diskman88/mpython-shield1/1_Hardware/V1.3/V1.3/掌控拓展板Ⅰ V1.2.pdf

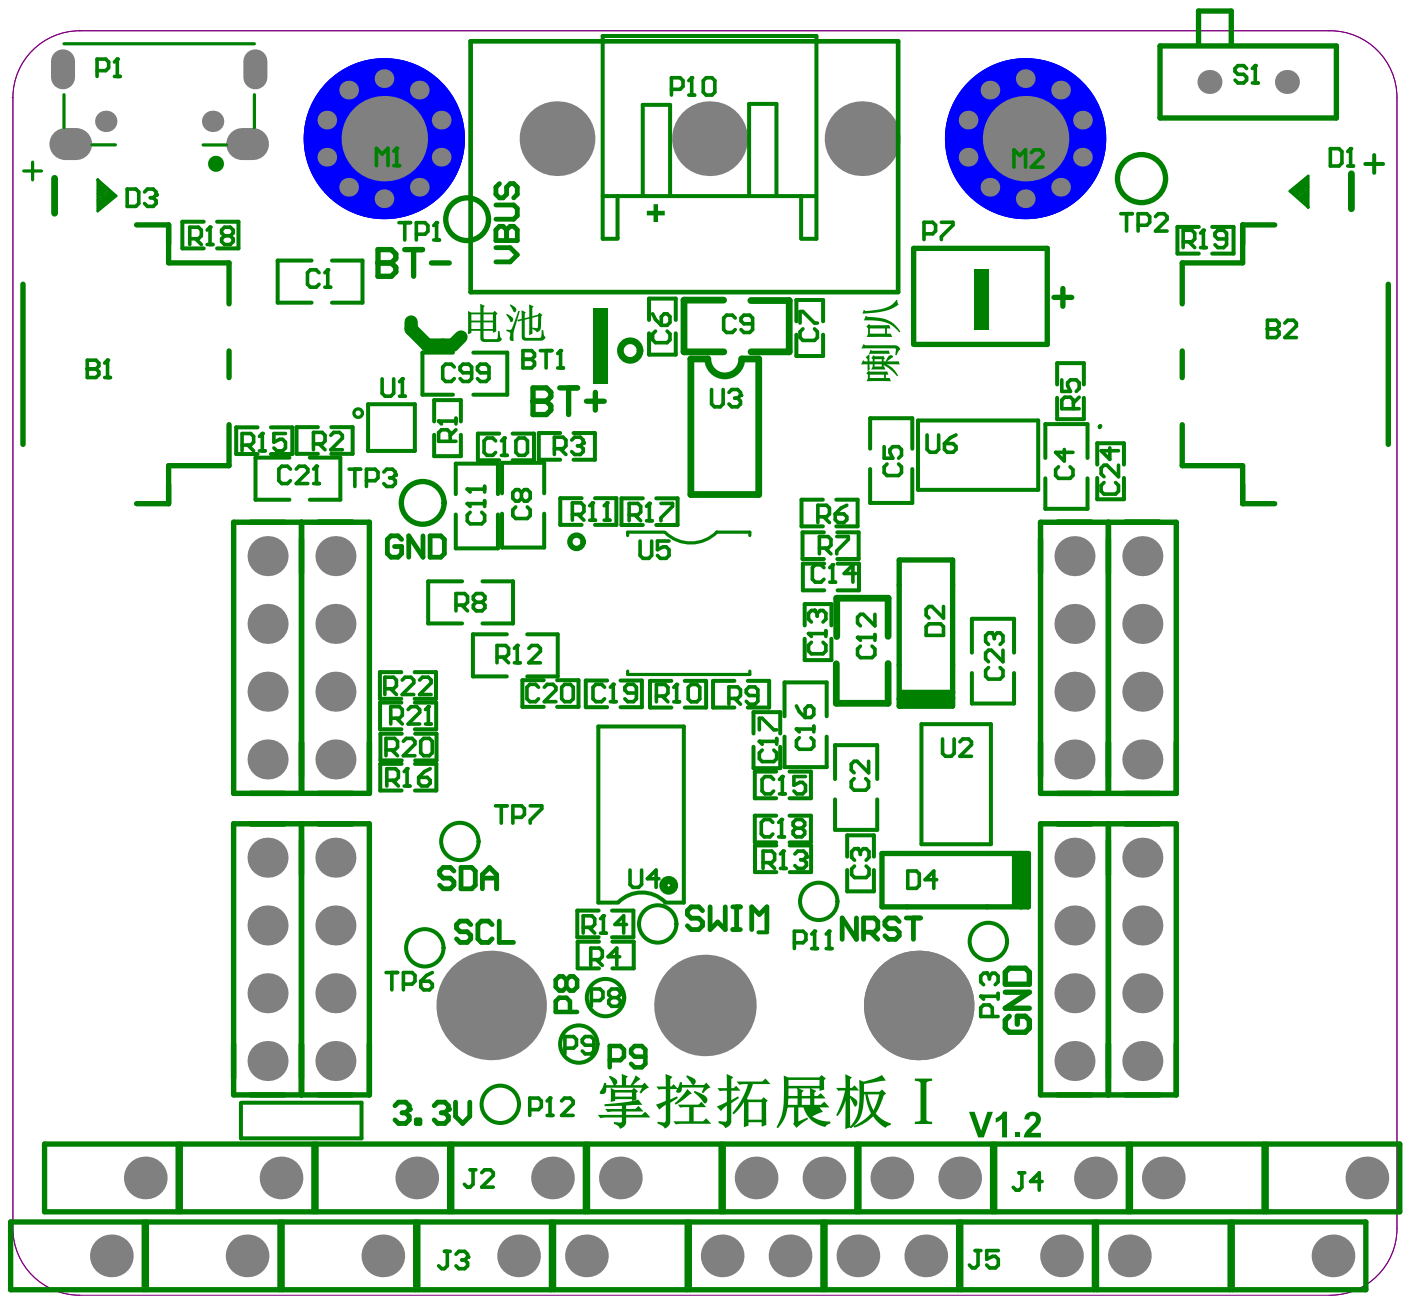
[picture p17: page 1]
