diskman88/mpython-shield1/1_Hardware/V1.4/V1.4/掌控拓展板Ⅰ V1.4.pdf

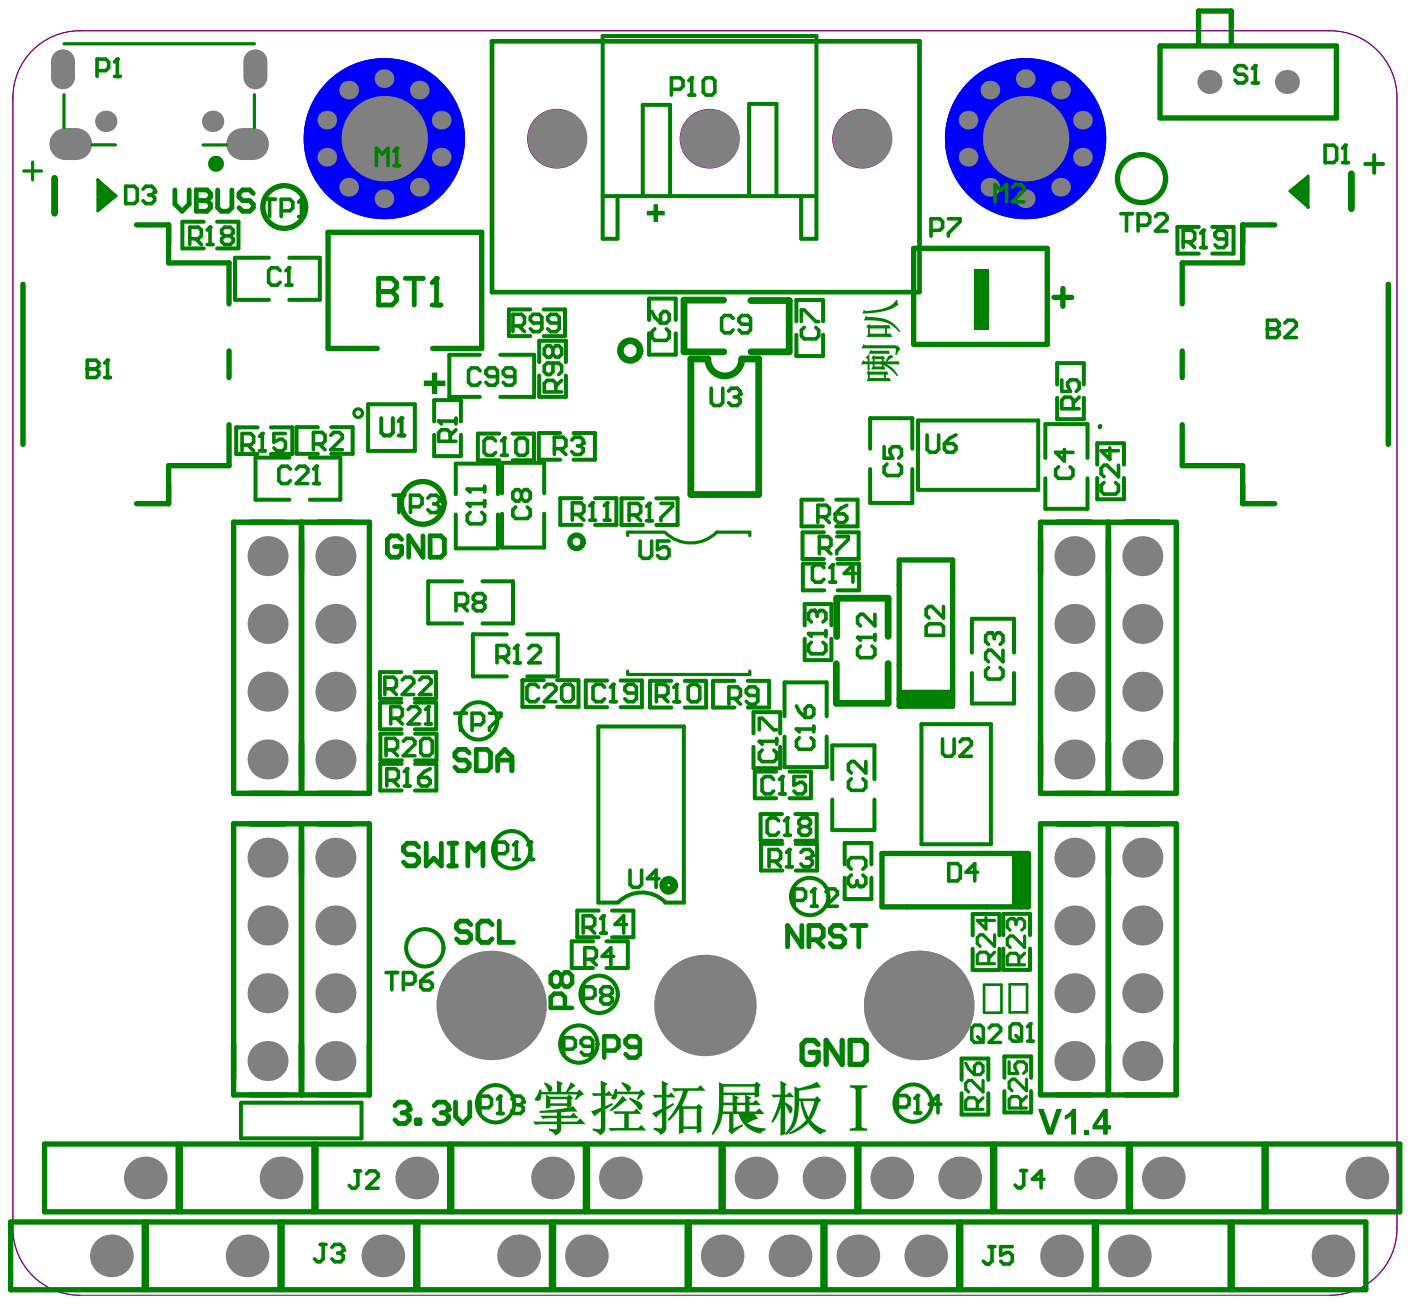
[picture p19: page 1]
